tuantdang/iotree/Source/IoTree_Intermittent/config.h

/*
 * config.h
 *
 *  Created on: Jul 6, 2021
 *      Author: Tuan Dang
 */


/*Board Selection*/
#define BOARD_IOTREE    1
//#define BOARD_TEETH     2

/* SENSOR */
#define SENSOR_ID       2

#define USE_MUL_SENSE_BLOCK   1


/*UART BUFFER*/
#define MAX_TX_BUF  (256)
#define MAX_RX_BUF  (MAX_TX_BUF)
